szymonPJO/SolderingStation-T12/PCB/soldering-mainboard-v1.0/simulation/LTspice_schematic.png

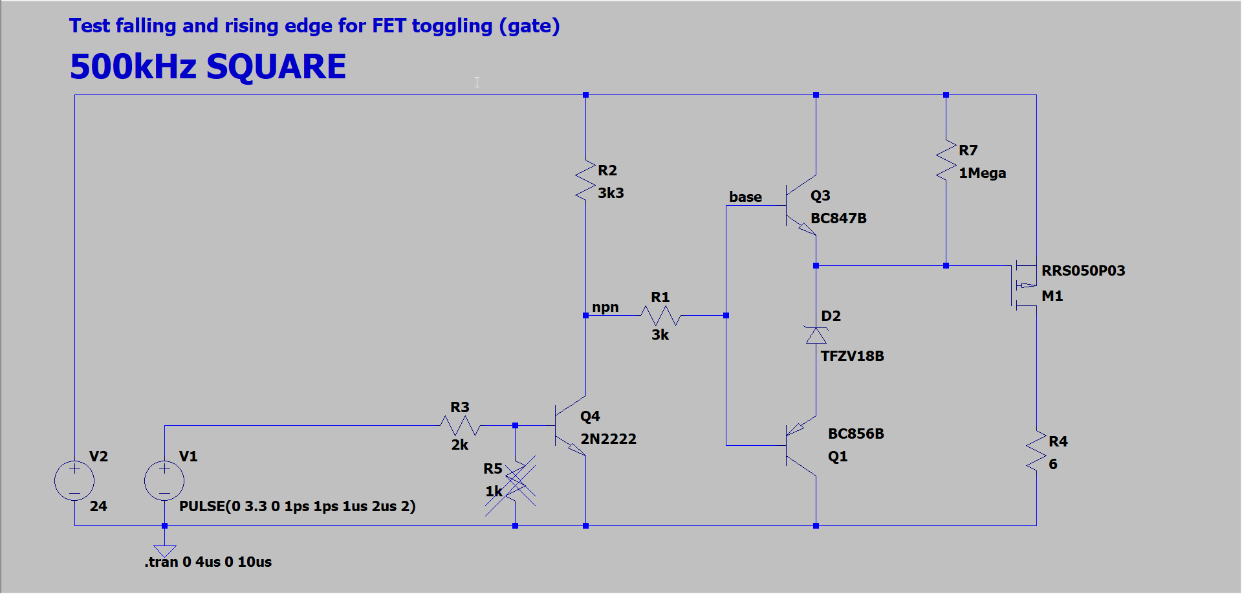
PCB/soldering-mainboard-v1.0/simulation/LTspice_schematic.png
