szymonPJO/SolderingStation-T12/Pictures/ADC-example_data.png

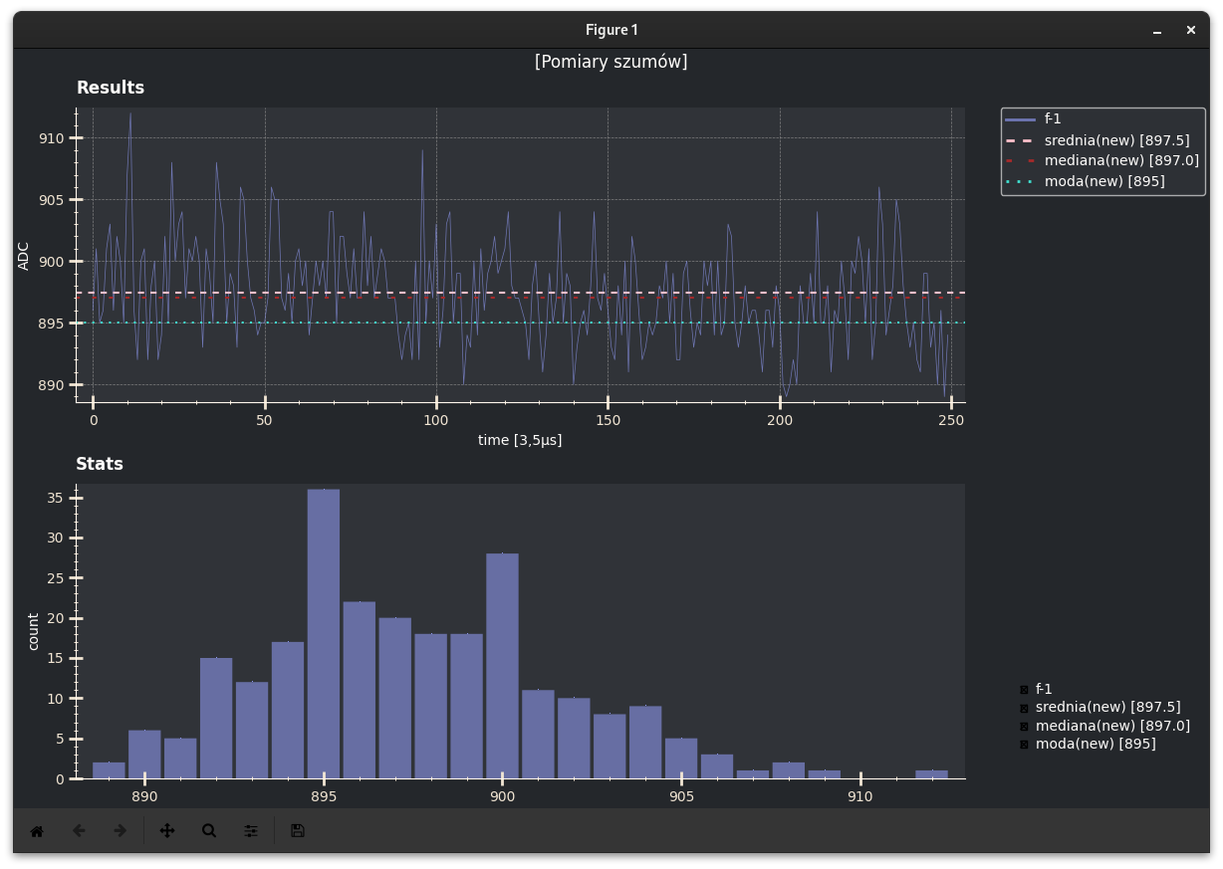
Pictures/ADC-example_data.png
