szymonPJO/SolderingStation-T12/Pictures/INA180_fig7-32.png

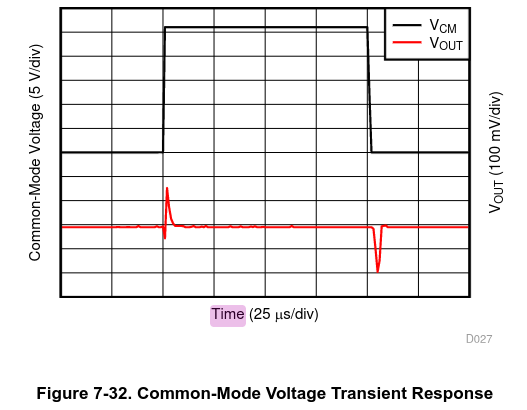
Pictures/INA180_fig7-32.png
