szymonPJO/SolderingStation-T12/Pictures/Photos/2023-07-09-20-47-13-878.jpg

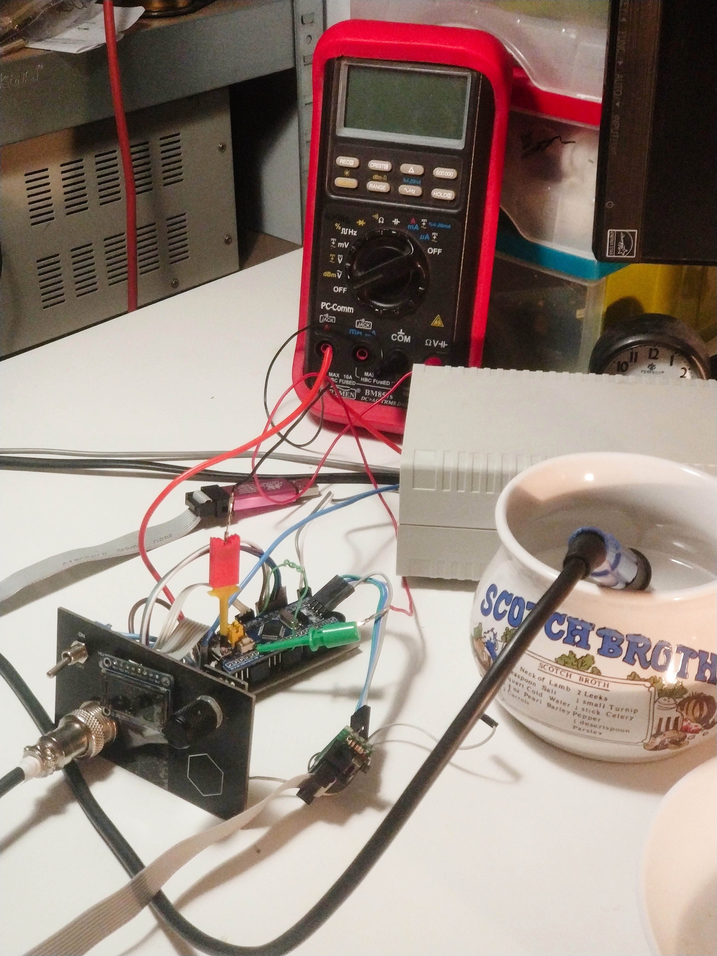
Pictures/Photos/2023-07-09-20-47-13-878.jpg
