szymonPJO/SolderingStation-T12/Pictures/Photos/2023-07-24-14-02-30-445.jpg

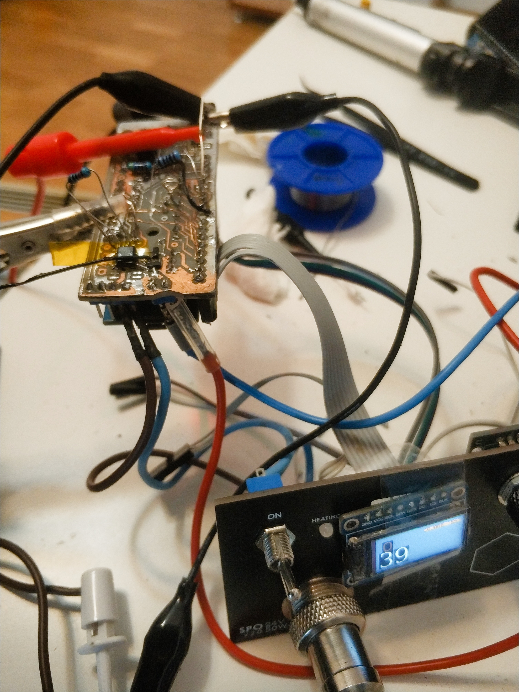
Pictures/Photos/2023-07-24-14-02-30-445.jpg
