szymonPJO/SolderingStation-T12/Pictures/Photos/2023-08-19-16-40-43-997.jpg

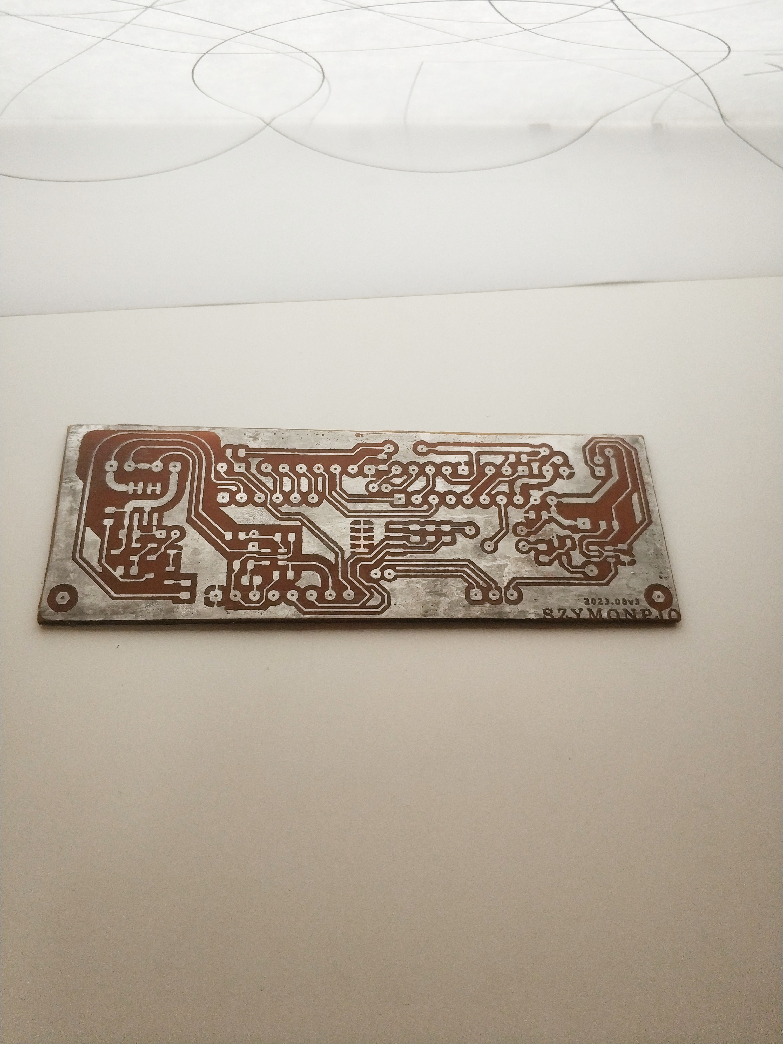
Pictures/Photos/2023-08-19-16-40-43-997.jpg
