szymonPJO/SolderingStation-T12/Pictures/Photos/2023-08-19-16-41-51-716.jpg

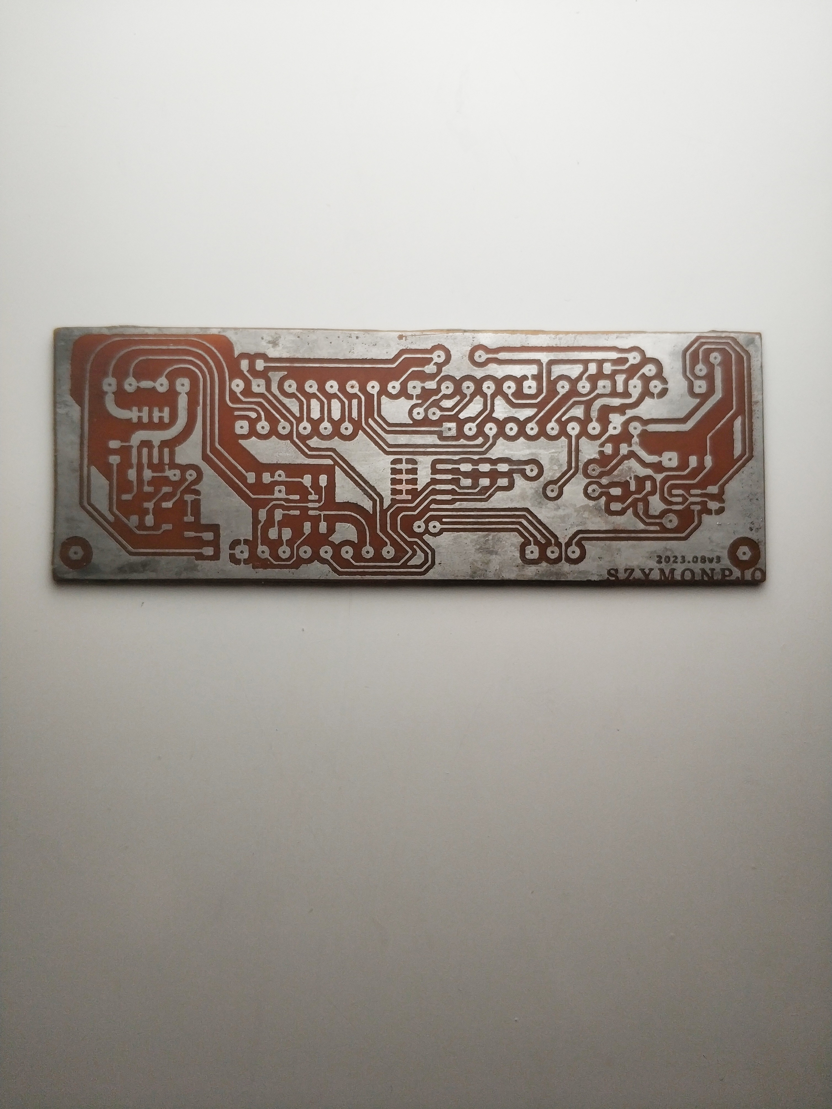
Pictures/Photos/2023-08-19-16-41-51-716.jpg
