szymonPJO/SolderingStation-T12/Pictures/Photos/2023-08-19-16-47-57-296.jpg

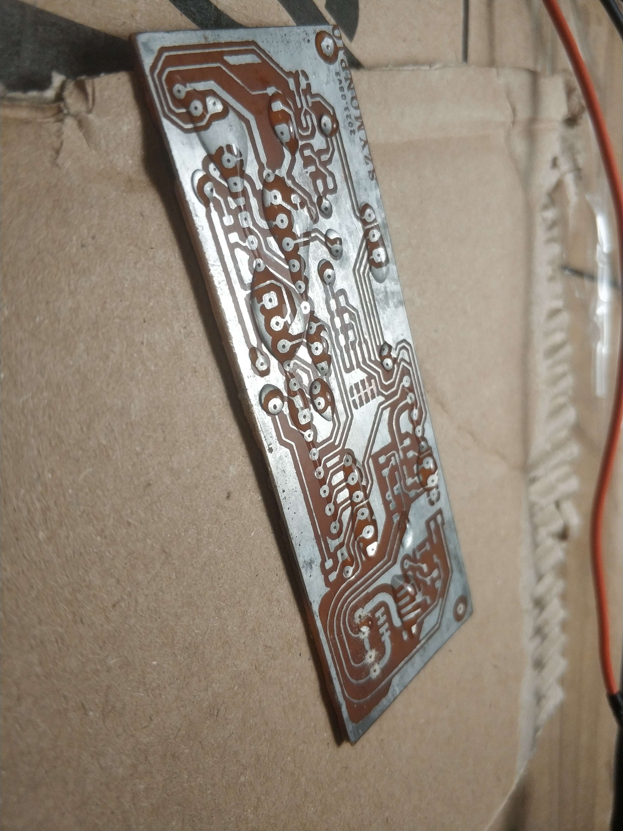
Pictures/Photos/2023-08-19-16-47-57-296.jpg
