szymonPJO/SolderingStation-T12/Pictures/Photos/2023-08-19-17-10-47-174.jpg

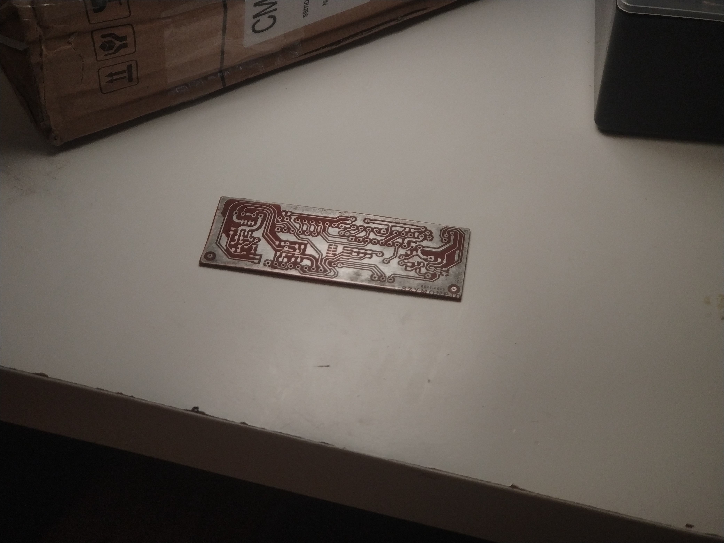
Pictures/Photos/2023-08-19-17-10-47-174.jpg
