szymonPJO/SolderingStation-T12/Pictures/Photos/2023-08-19-17-11-17-230(PCB-drilled).jpg

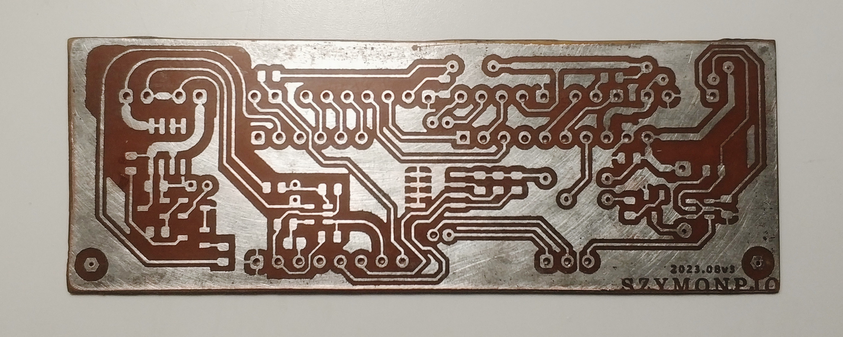
Pictures/Photos/2023-08-19-17-11-17-230(PCB-drilled).jpg
