szymonPJO/SolderingStation-T12/Pictures/Photos/2023-08-19-17-29-24-759.jpg

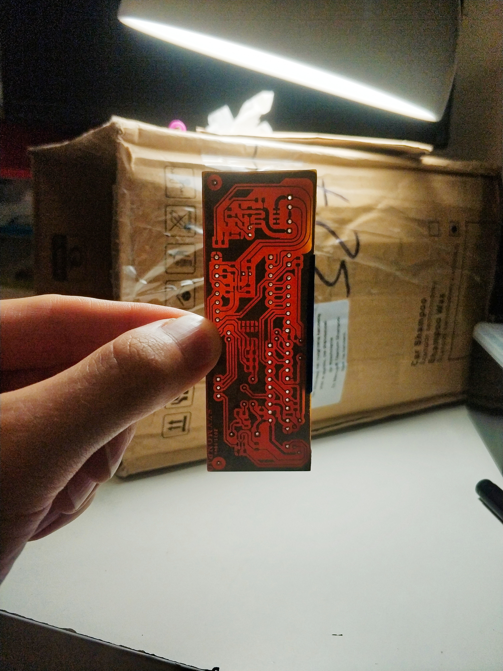
Pictures/Photos/2023-08-19-17-29-24-759.jpg
