szymonPJO/SolderingStation-T12/Pictures/Photos/2023-08-21-18-47-29-080.jpg

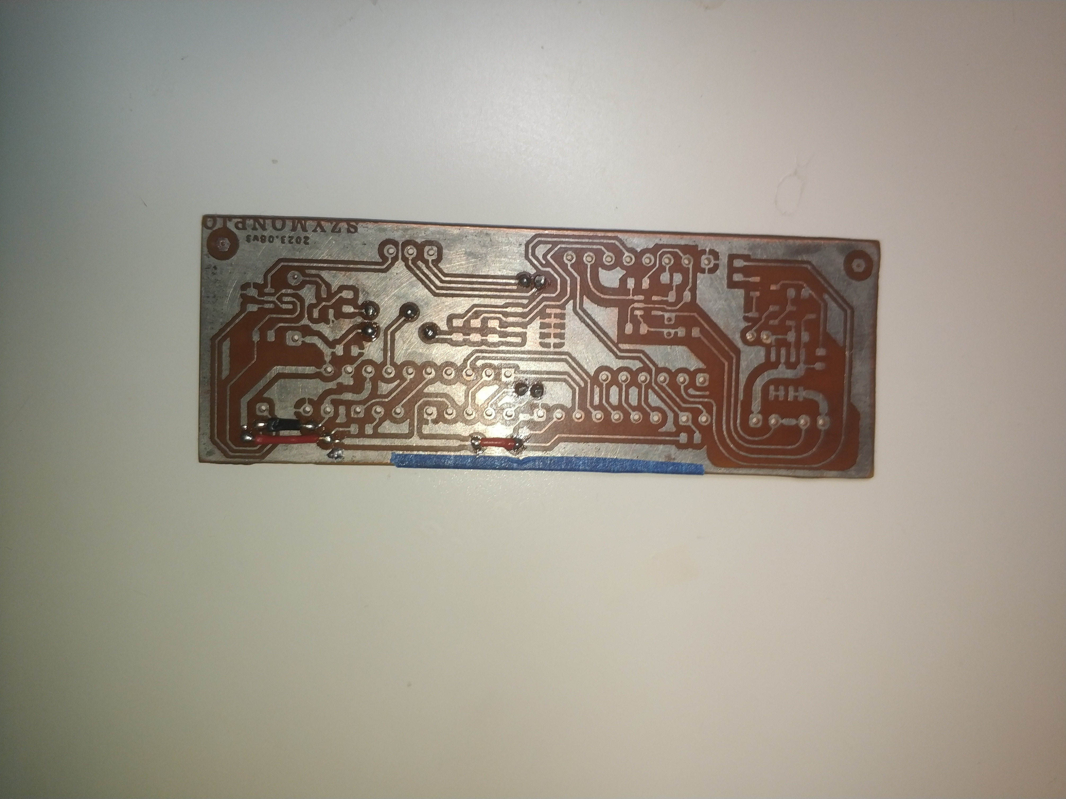
Pictures/Photos/2023-08-21-18-47-29-080.jpg
