szymonPJO/SolderingStation-T12/Pictures/Photos/2023-08-23-18-42-50-305.jpg

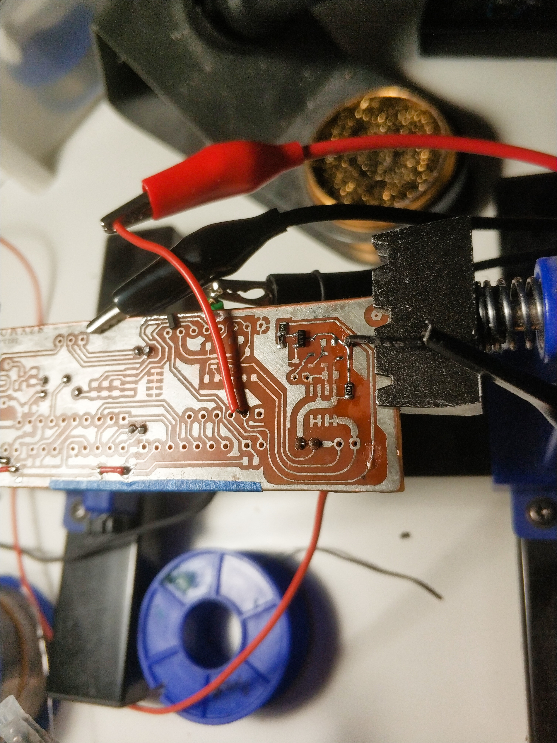
Pictures/Photos/2023-08-23-18-42-50-305.jpg
