szymonPJO/SolderingStation-T12/Pictures/Photos/2023-08-23-18-43-02-561.jpg

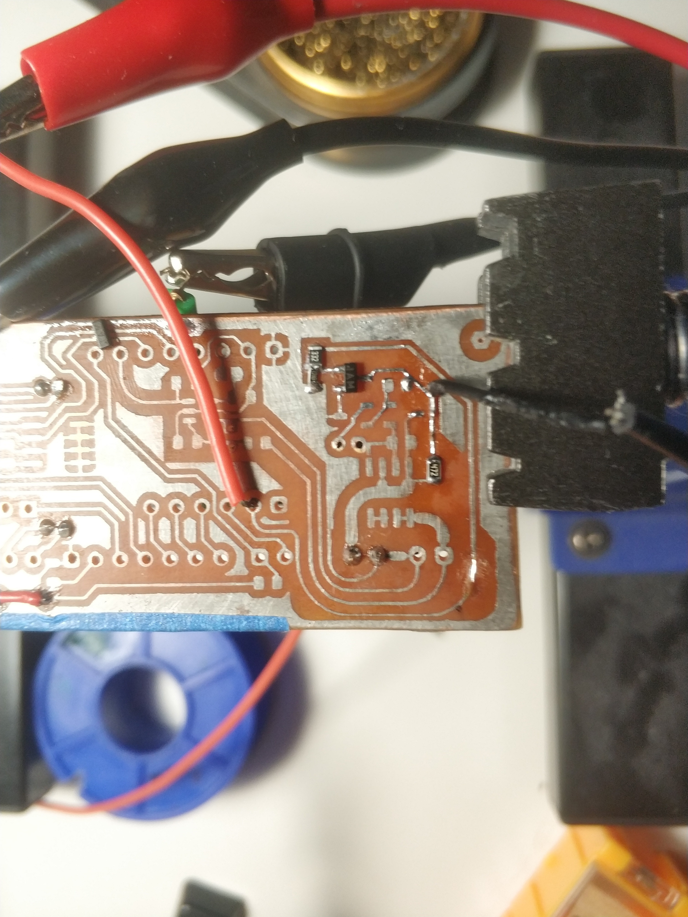
Pictures/Photos/2023-08-23-18-43-02-561.jpg
