szymonPJO/SolderingStation-T12/Pictures/Photos/2024-02-14-23-16-59-233.jpg

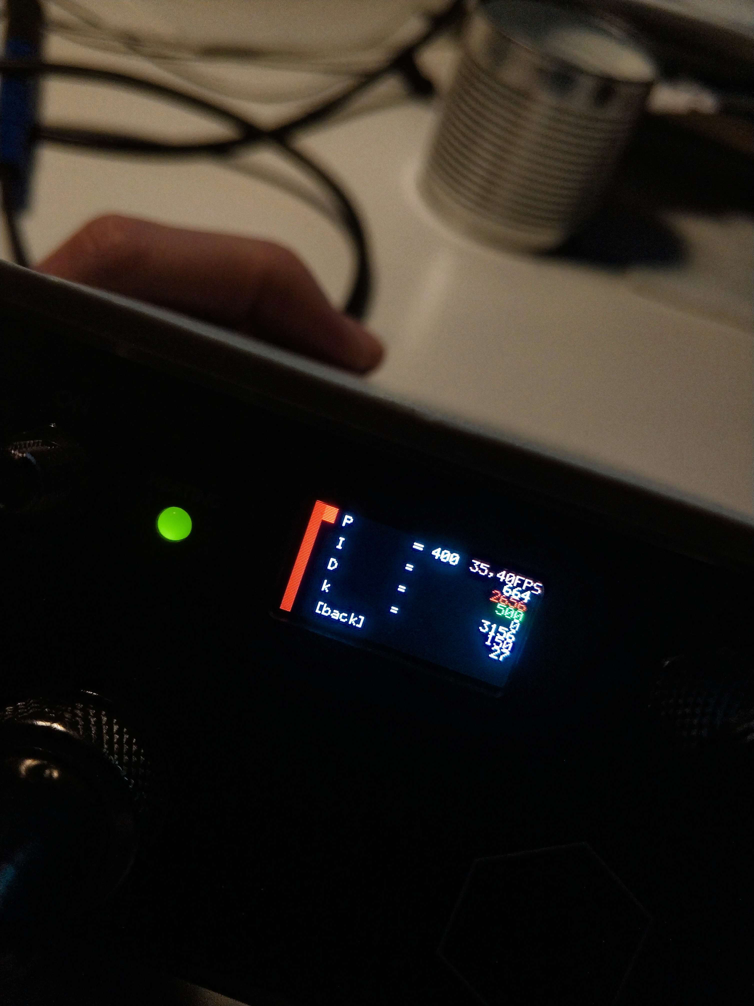
Pictures/Photos/2024-02-14-23-16-59-233.jpg
