szymonPJO/SolderingStation-T12/Pictures/Photos/2024-02-21-18-42-24-807.jpg

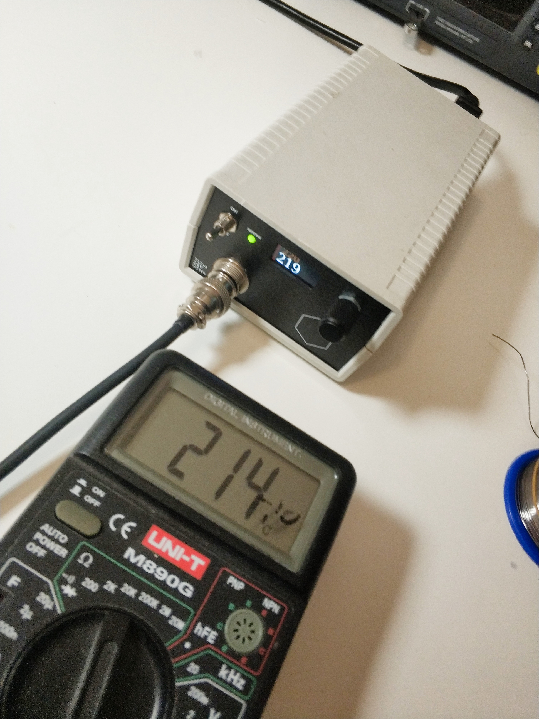
Pictures/Photos/2024-02-21-18-42-24-807.jpg
