szymonPJO/SolderingStation-T12/Pictures/Photos/2024-02-21-18-54-16-767.jpg

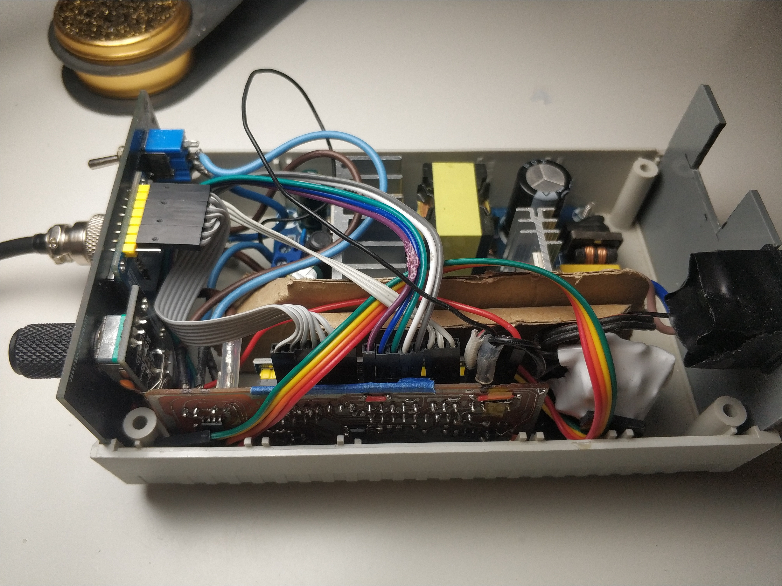
Pictures/Photos/2024-02-21-18-54-16-767.jpg
