szymonPJO/SolderingStation-T12/Pictures/Photos/2024-02-21-19-19-47-465.jpg

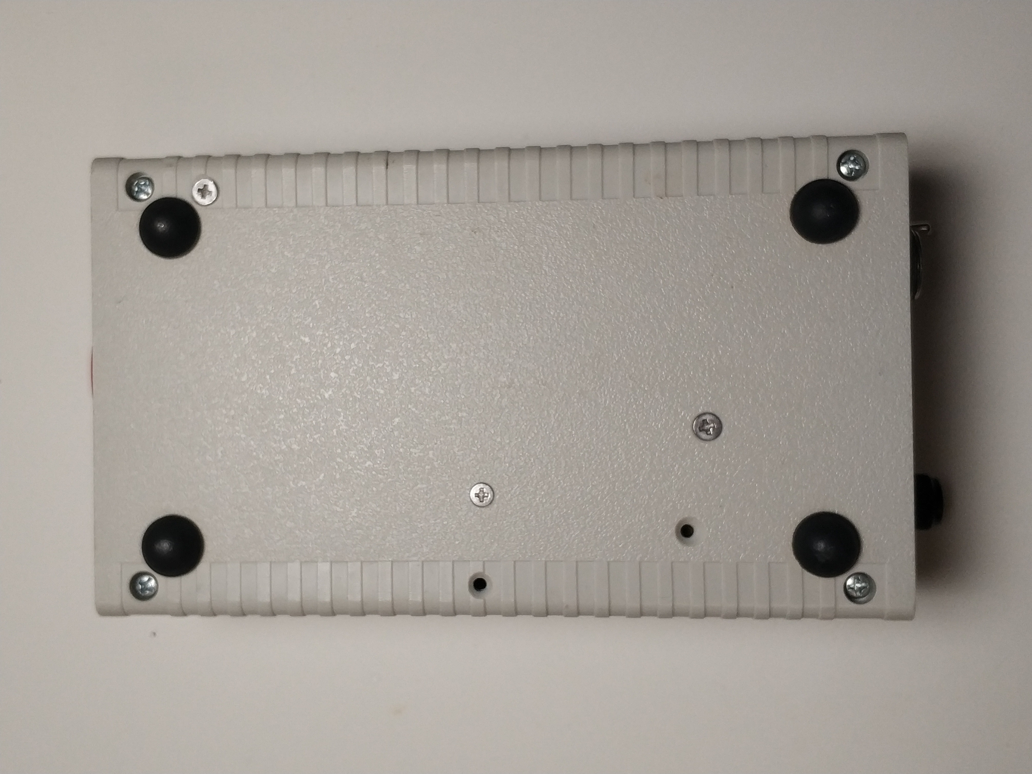
Pictures/Photos/2024-02-21-19-19-47-465.jpg
