szymonPJO/SolderingStation-T12/Pictures/Photos/IMG_20240221_181312.jpg

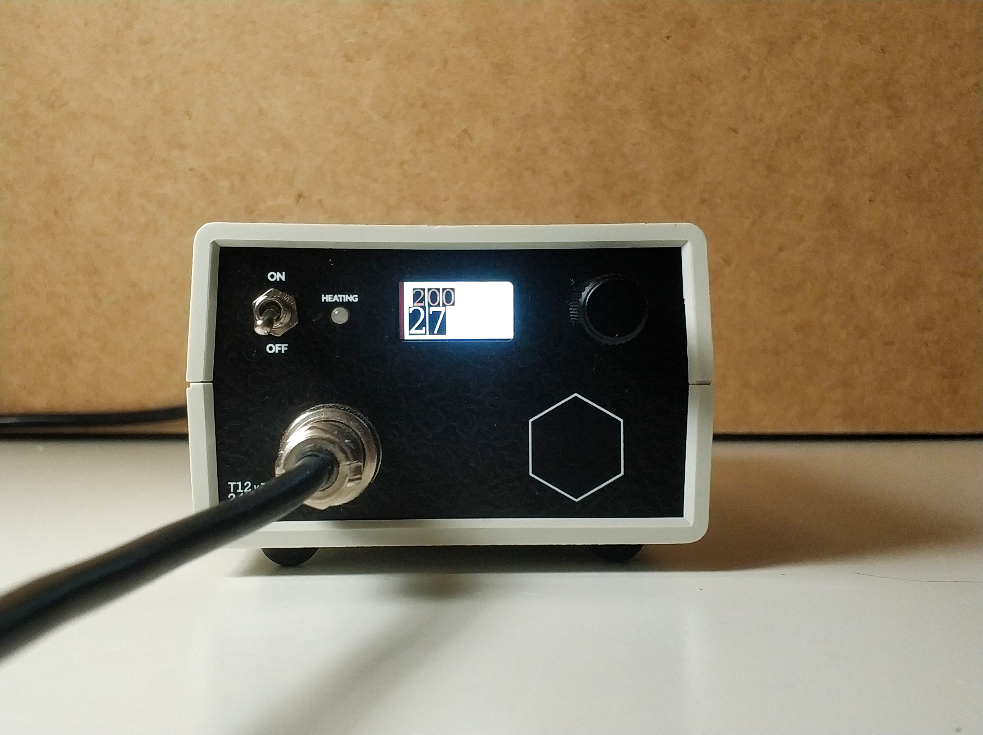
Pictures/Photos/IMG_20240221_181312.jpg
