szymonPJO/SolderingStation-T12/Pictures/Photos/IMG_20240221_182525.jpg

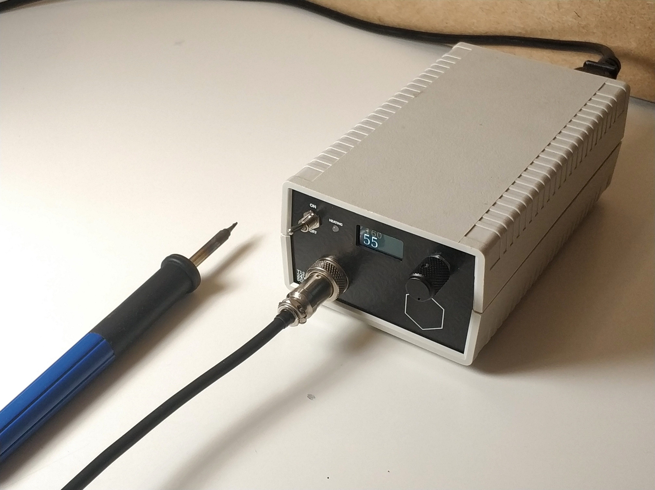
Pictures/Photos/IMG_20240221_182525.jpg
