szymonPJO/SolderingStation-T12/Pictures/Photos/IMG_20240221_182904.jpg

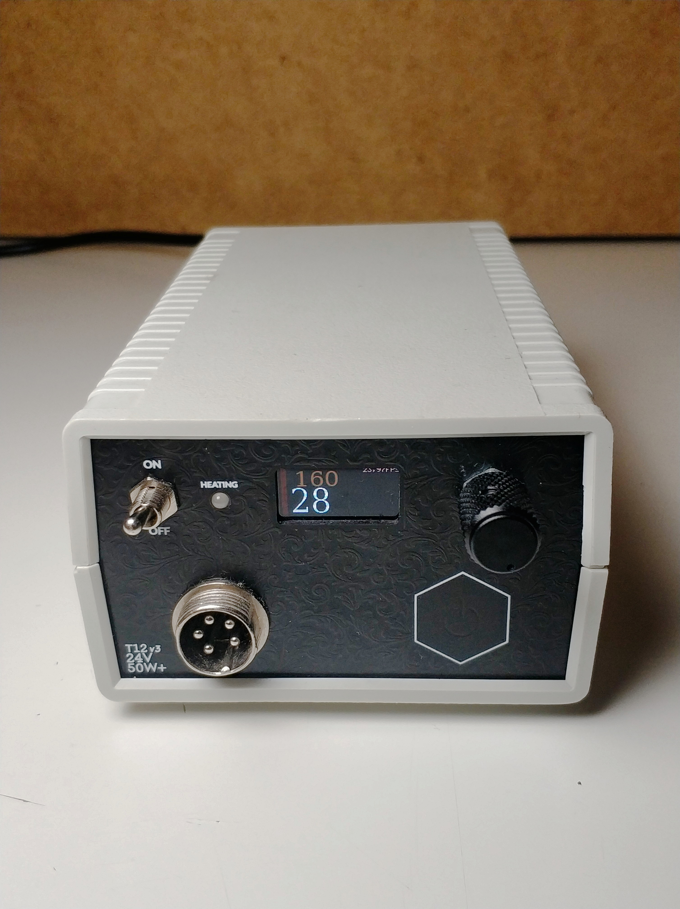
Pictures/Photos/IMG_20240221_182904.jpg
