szymonPJO/SolderingStation-T12/Pictures/Photos/IMG_20240221_183115.jpg

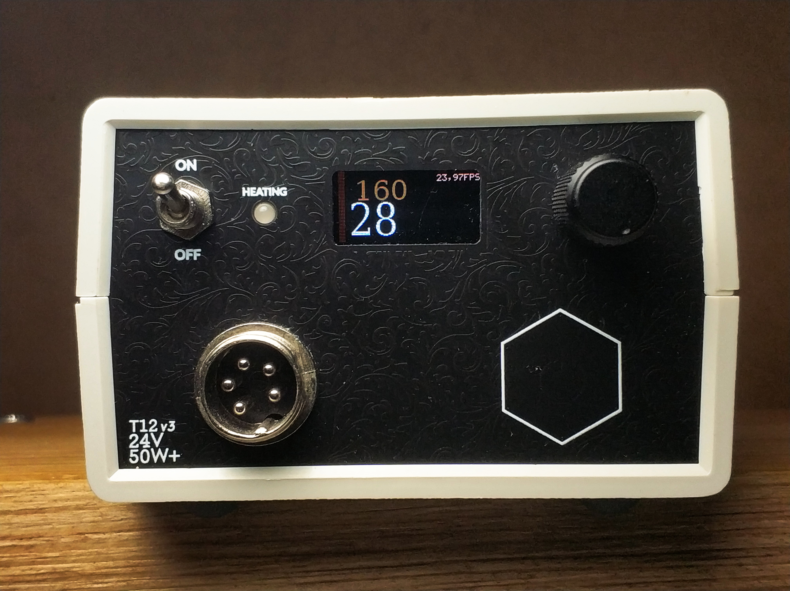
Pictures/Photos/IMG_20240221_183115.jpg
