szymonPJO/SolderingStation-T12/Pictures/Photos/inside-the-box01.jpg

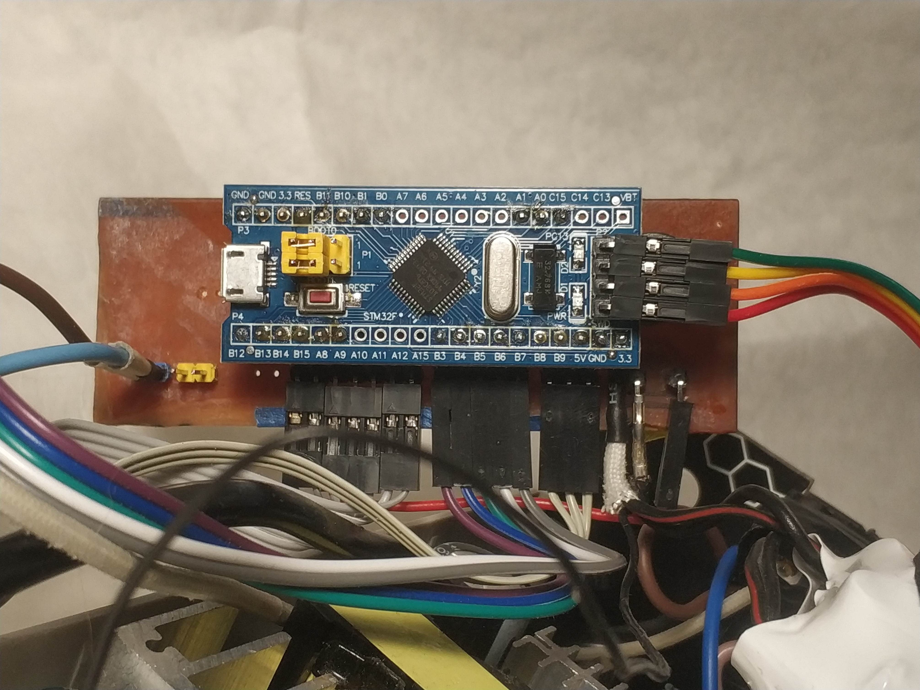
Pictures/Photos/inside-the-box01.jpg
