szymonPJO/SolderingStation-T12/Pictures/Photos/inside-the-box02.jpg

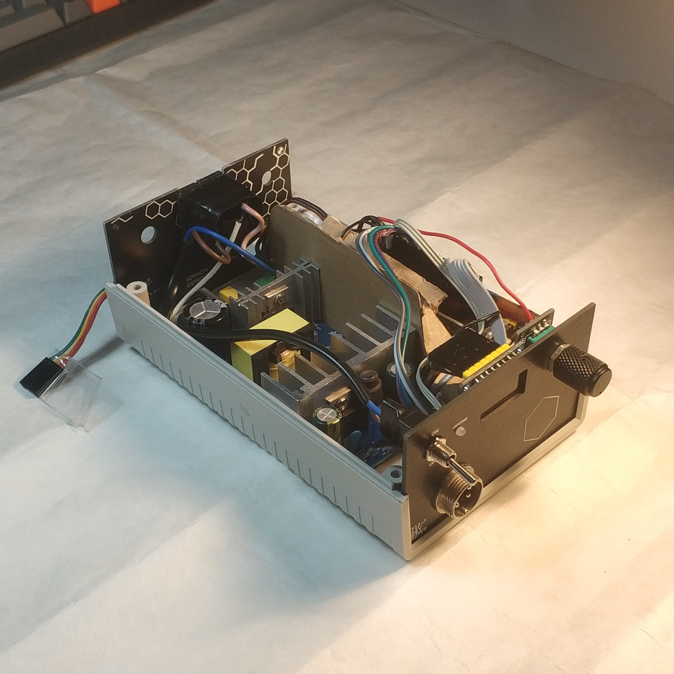
Pictures/Photos/inside-the-box02.jpg
