szymonPJO/SolderingStation-T12/Pictures/Photos/inside-the-box03.jpg

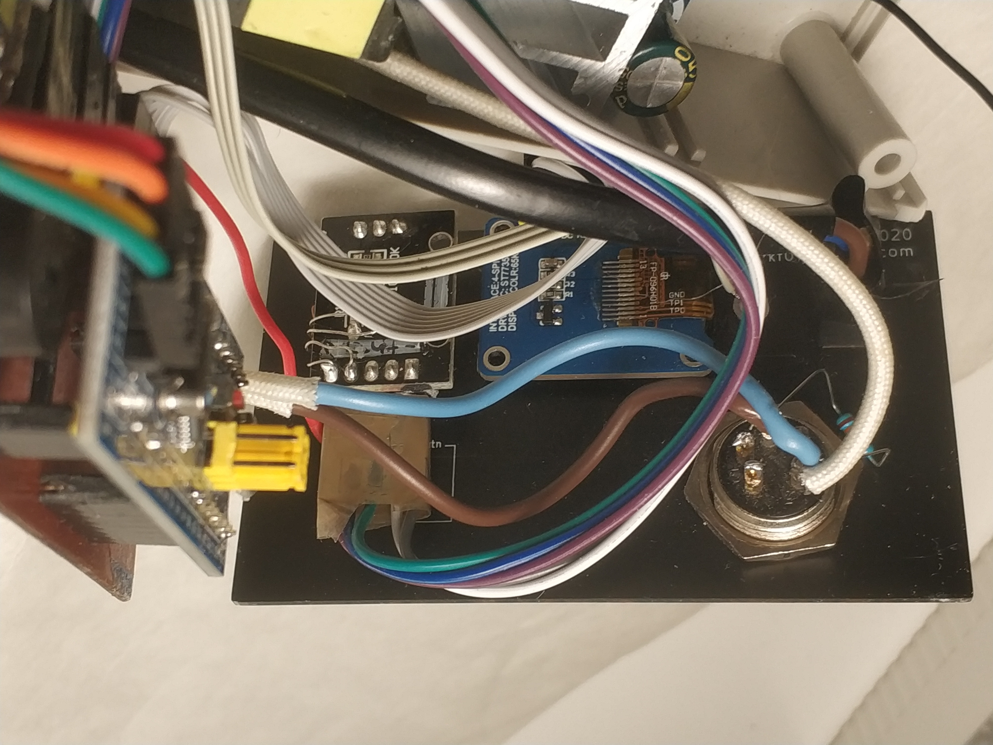
Pictures/Photos/inside-the-box03.jpg
