szymonPJO/SolderingStation-T12/Pictures/Photos/inside-the-box04.jpg

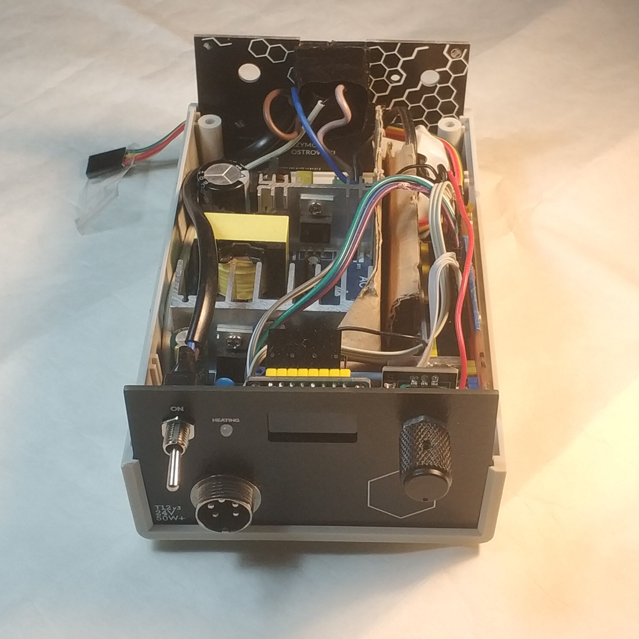
Pictures/Photos/inside-the-box04.jpg
