szymonPJO/SolderingStation-T12/Pictures/Photos/inside-the-box05.jpg

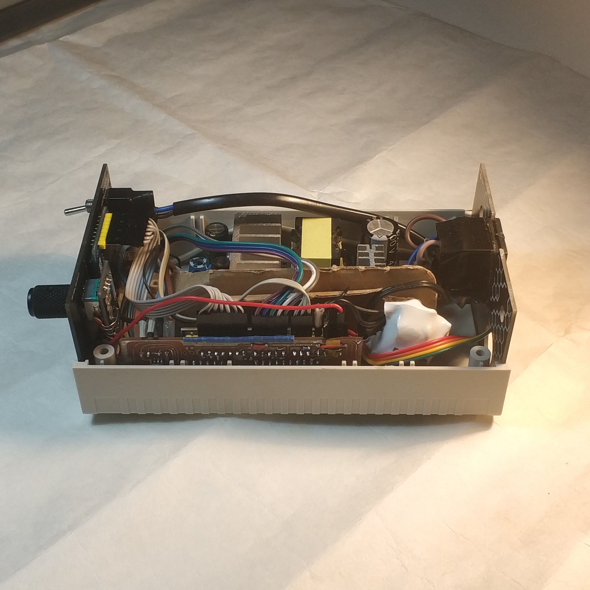
Pictures/Photos/inside-the-box05.jpg
