szymonPJO/SolderingStation-T12/Pictures/Photos/inside-the-box06.jpg

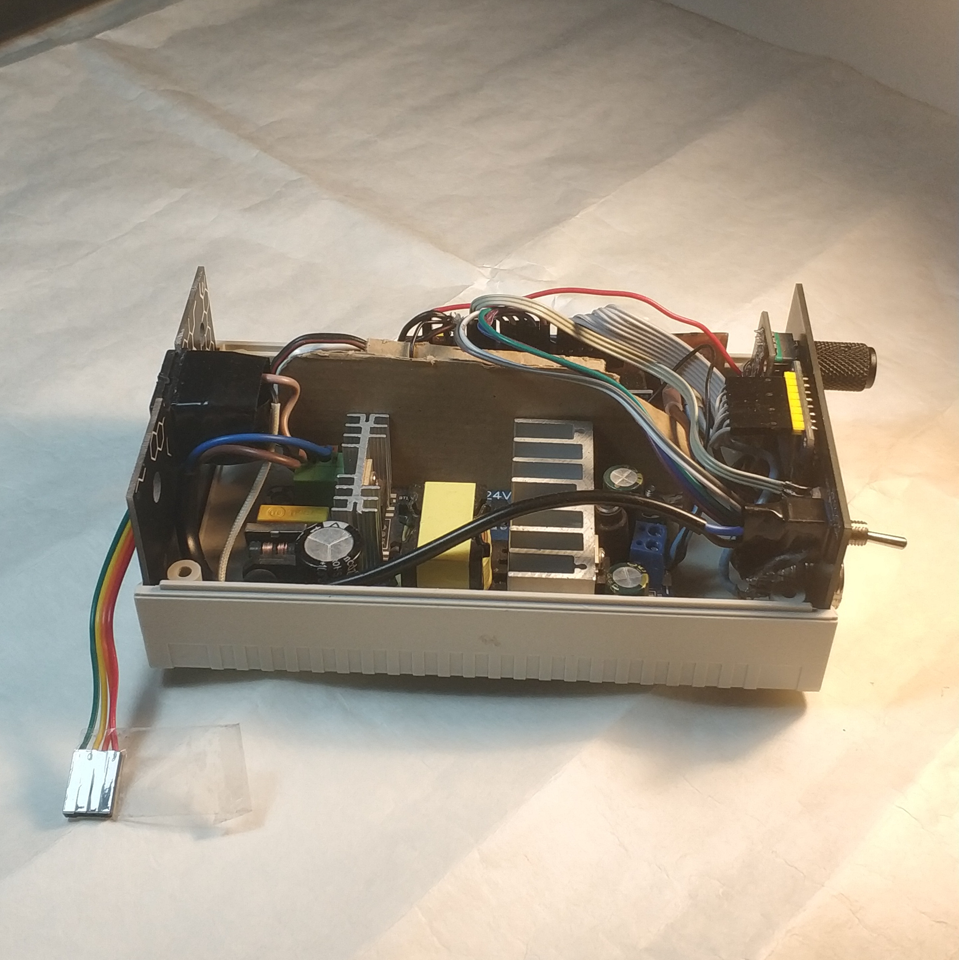
Pictures/Photos/inside-the-box06.jpg
