szymonPJO/SolderingStation-T12/Pictures/Photos/inside-the-box07.jpg

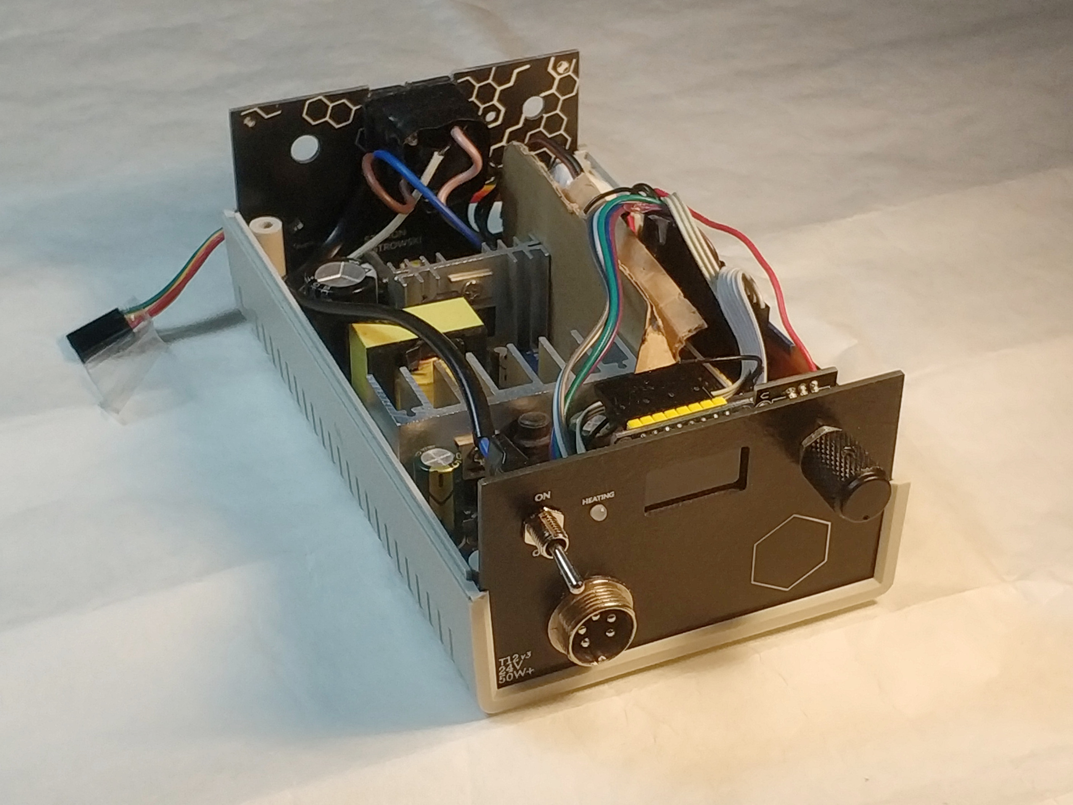
Pictures/Photos/inside-the-box07.jpg
