szymonPJO/SolderingStation-T12/Pictures/Photos/inside-the-box08.jpg

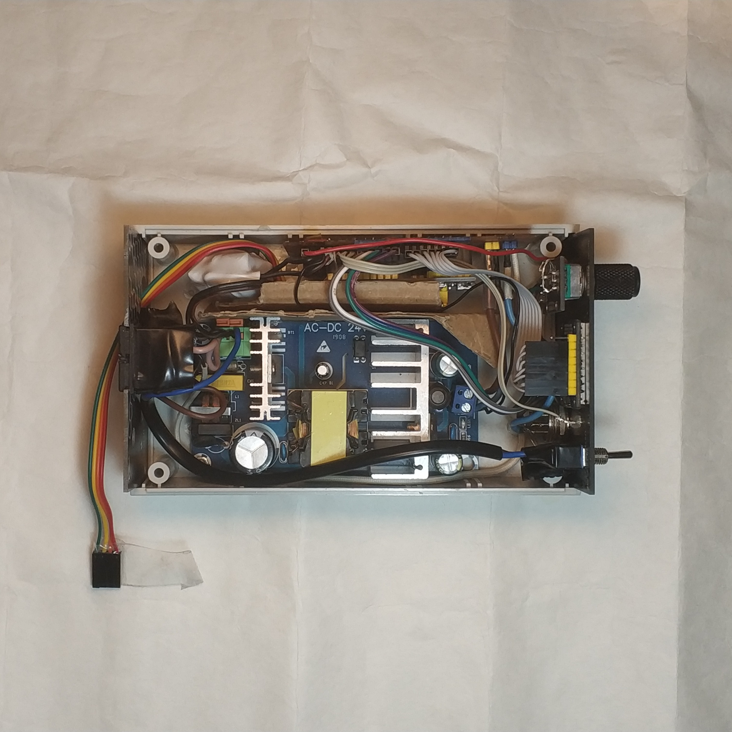
Pictures/Photos/inside-the-box08.jpg
