szymonPJO/SolderingStation-T12/Pictures/Photos/OPAMP-out-while-growing-temp.gif

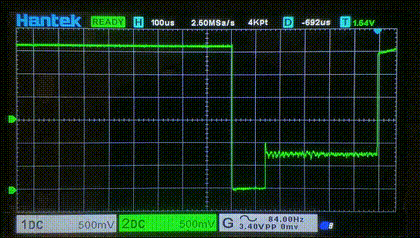
Pictures/Photos/OPAMP-out-while-growing-temp.gif
