szymonPJO/SolderingStation-T12/Pictures/PID(P=1,5 I=1,5)-example_data.png

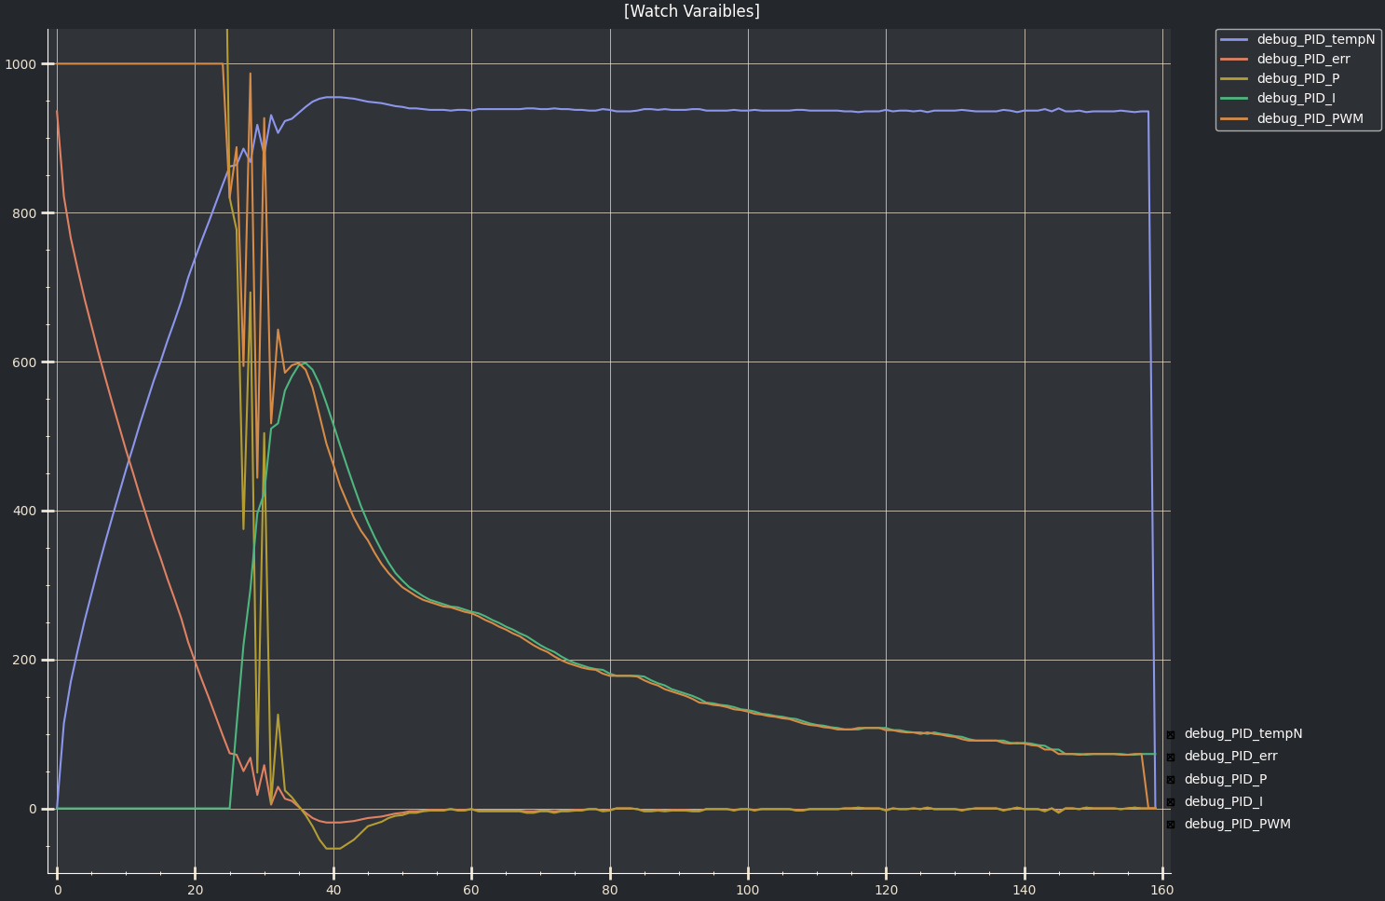
Pictures/PID(P=1,5 I=1,5)-example_data.png
