szymonPJO/SolderingStation-T12/PCB/soldering-mainboard-v1.0/measurement/PCB_montage/Q2_Base-Q2_CollectorMem(3K3+1K).bmp

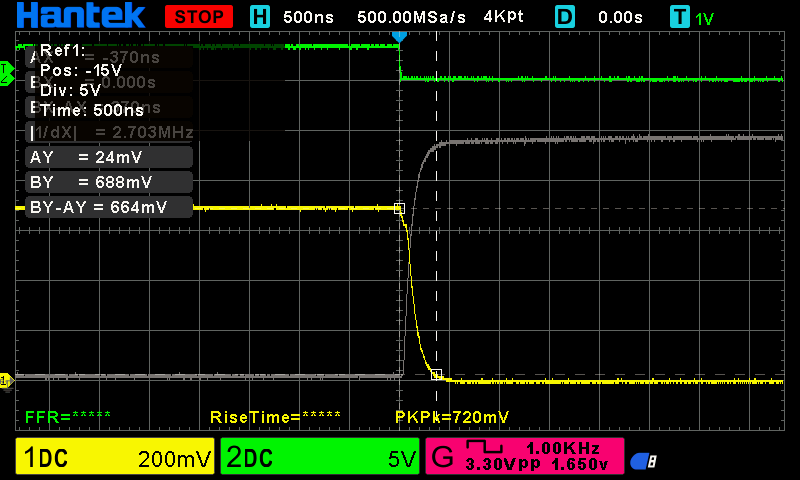
PCB/soldering-mainboard-v1.0/measurement/PCB_montage/Q2_Base-Q2_CollectorMem(3K3+1K).bmp
