szymonPJO/SolderingStation-T12/PCB/soldering-mainboard-v1.0/measurement/PCB_montage/Q2_Collector(Base3K3_Collector4K7).bmp

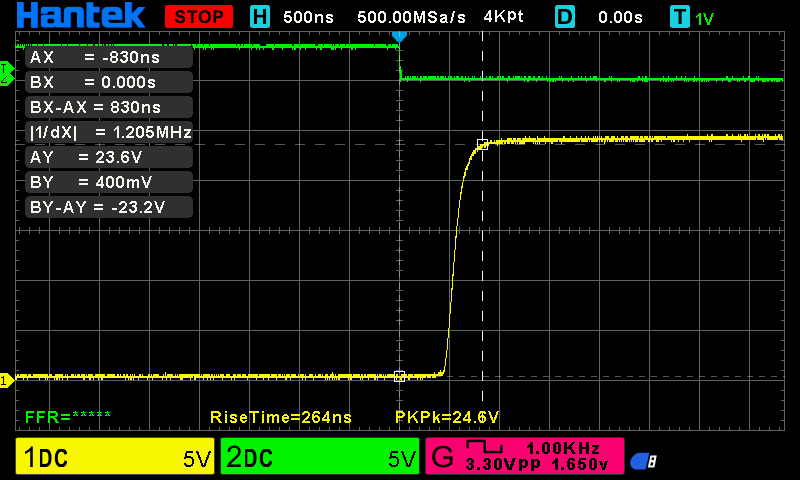
PCB/soldering-mainboard-v1.0/measurement/PCB_montage/Q2_Collector(Base3K3_Collector4K7).bmp
