szymonPJO/SolderingStation-T12/PCB/soldering-mainboard-v1.0/simulation/LTspice_graph.png

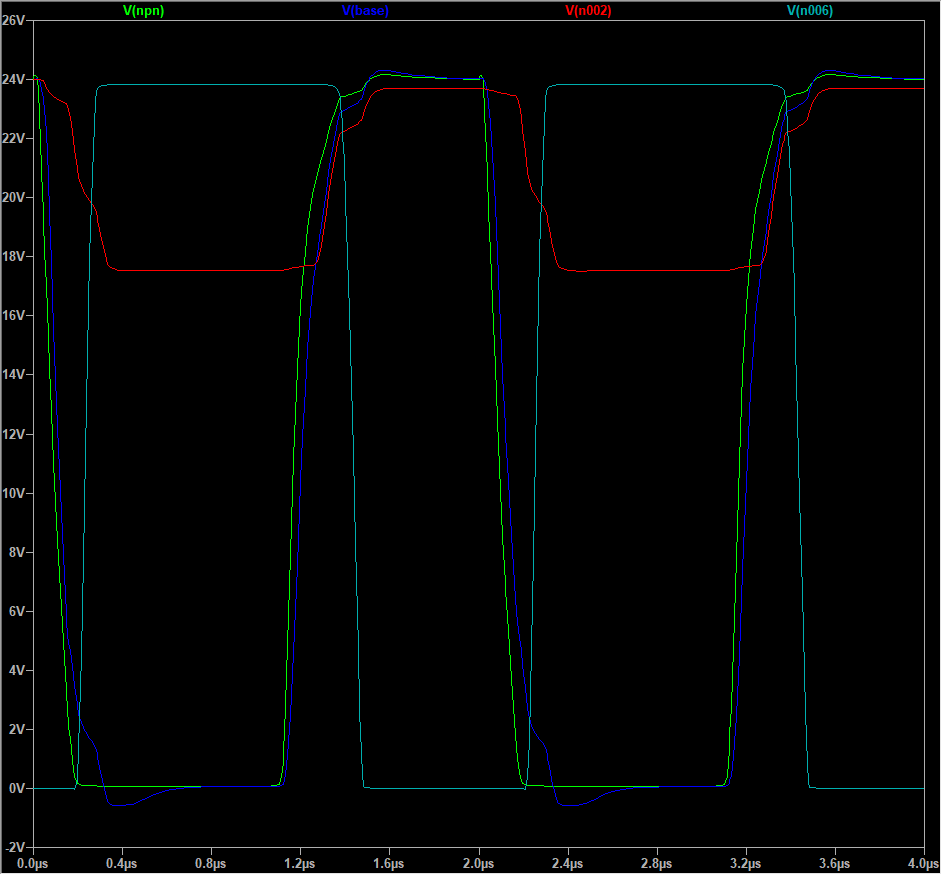
PCB/soldering-mainboard-v1.0/simulation/LTspice_graph.png
