szymonPJO/SolderingStation-T12/PCB/soldering-mainboard-v1.0/measurement/npn rising edge analisis/_WRONG_PWR(3V3)/MMBT3904L/dso_01_01_00_42_12.bmp

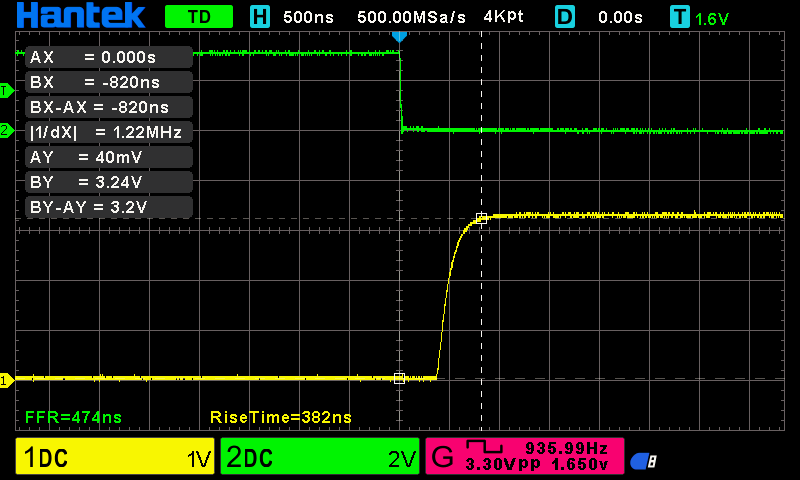
PCB/soldering-mainboard-v1.0/measurement/npn rising edge analisis/_WRONG_PWR(3V3)/MMBT3904L/dso_01_01_00_42_12.bmp
