szymonPJO/SolderingStation-T12/PCB/soldering-mainboard-v1.0/measurement/npn rising edge analisis/AFTER-330R_BASE_TO_GND(2N2222).bmp

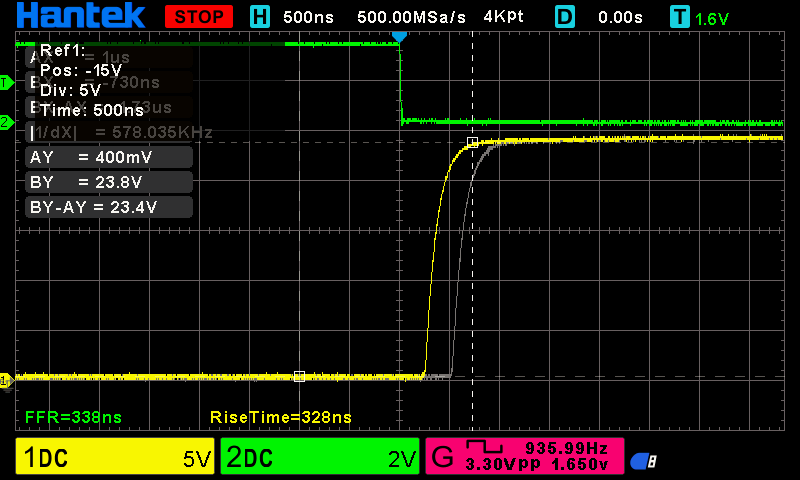
PCB/soldering-mainboard-v1.0/measurement/npn rising edge analisis/AFTER-330R_BASE_TO_GND(2N2222).bmp
