szymonPJO/SolderingStation-T12/PCB/soldering-mainboard-v1.0/measurement/npn rising edge analisis/BC547 (THT)/dso_01_01_00_10_08.bmp

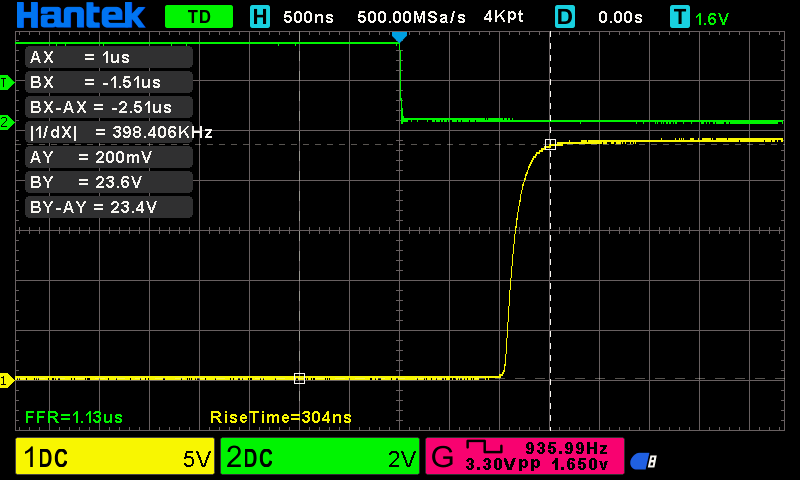
PCB/soldering-mainboard-v1.0/measurement/npn rising edge analisis/BC547 (THT)/dso_01_01_00_10_08.bmp
