szymonPJO/SolderingStation-T12/PCB/soldering-mainboard-v1.0/measurement/npn rising edge analisis/MAX(dzielnik).bmp

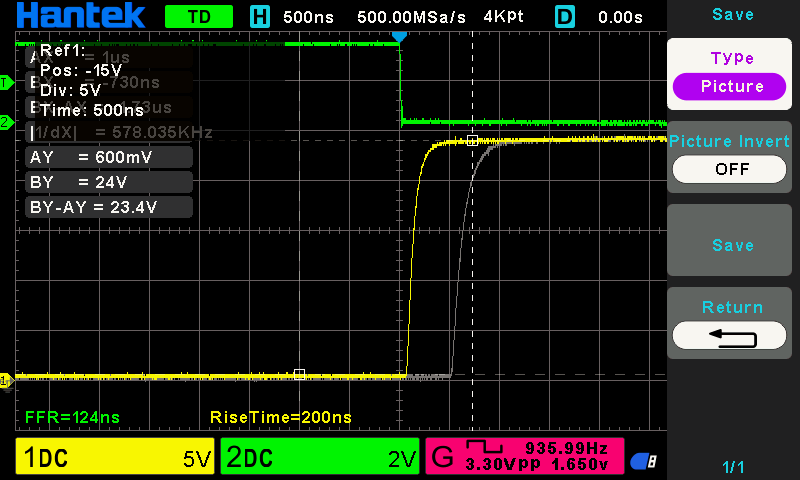
PCB/soldering-mainboard-v1.0/measurement/npn rising edge analisis/MAX(dzielnik).bmp
