szymonPJO/SolderingStation-T12/PCB/soldering-mainboard-v1.0/measurement/V-I_Curve_NPN_B-E.jpeg

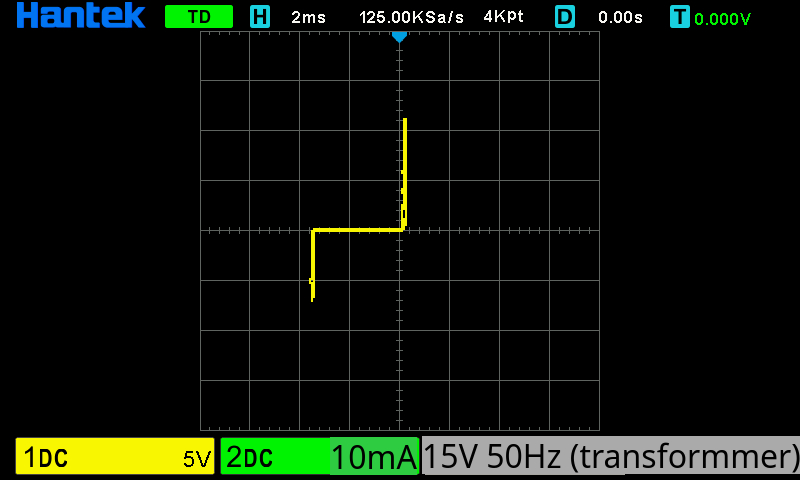
PCB/soldering-mainboard-v1.0/measurement/V-I_Curve_NPN_B-E.jpeg
