szymonPJO/SolderingStation-T12/Pictures/errata i2c and remapped spi1 conflict.JPG

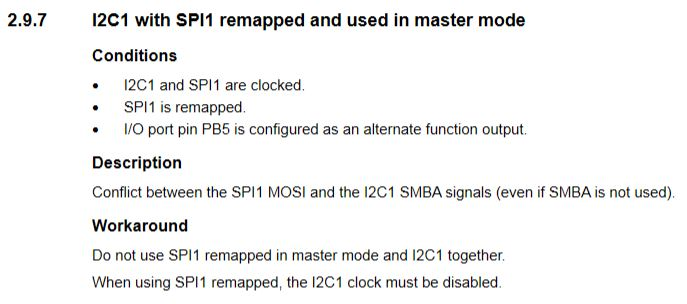
Pictures/errata i2c and remapped spi1 conflict.JPG
