szymonPJO/SolderingStation-T12/PCB/soldering-mainboard-v1.0/simulation/pwm-soldering-500kHz(original).asc

D2: zener; TFZV18B
M1: pmos; RRS050P03
Q1: pnp; BC856B
Q3: npn; BC847B
Q4: npn; 2N2222
R1: res; 3k
R2: res; 3k3
R3: res; 2k
R4: res; 6
R5: res; 1k
R7: res; 1Mega
V1: voltage; PULSE(0 3.3 0 1ps 1ps 1us 2us 2)
V2: voltage; 24
Named nets: 0, npn, base
.tran 0 4us 0 10us
500kHz SQUARE
Test falling and rising edge for FET toggling (gate)
